emeb/orangecrab_adc/gateware/verilog/src/tuner_slice_1k.v

// tuner_slice_1k.v - one leg of real->complex tuner with 4k sine cycle
// 07-18-16 E. Brombaugh

module tuner_slice_1k #(
    parameter dsz = 14,
              psz = 12
)
(
    input clk, reset, shf_90,
    input signed [dsz-1:0] in,
    input [psz-1:0] phs,
    output reg signed [dsz-1:0] out
);
    // split acc into quadrant and address and delay sign bit
    wire [1:0] p_quad = phs[psz-1:psz-2] + {1'b0,shf_90};
    reg [1:0] quad;
    reg [psz-3:0] addr;
    reg sincos_sign;
    always @(posedge clk)
    begin
        if(reset == 1'b1)
        begin
            quad <= 2'b0;
            addr <= 8'b0;
            sincos_sign <= 1'b0;
        end
        else
        begin
            quad <= p_quad;
            addr <= phs[psz-3:0] ^ {psz-2{p_quad[0]}};
            sincos_sign <= quad[1];
        end
    end
    
    // look up 1/4 cycle sine
    reg signed [15:0] sine_lut[0:1023];
    reg signed [15:0] sincos_raw;
    initial
    begin
        $readmemh("../src/sine_table_1k.memh", sine_lut);
    end
    always @(posedge clk)
    begin
        sincos_raw <= sine_lut[addr];
    end
    
    // invert sign of lut output and delay to align
    reg signed [15:0] sincos_p, sincos;
    reg sincos_sign_d1;
    always @(posedge clk)
    begin
        if(reset == 1'b1)
        begin
            sincos <= 16'h0000;
            sincos_p <= 16'h0000;
            sincos_sign_d1 <= 0;
        end
        else
        begin
            sincos_sign_d1 <= sincos_sign;
            sincos_p <= sincos_raw;
            sincos <= sincos_sign_d1 ? -sincos_p : sincos_p;
        end
    end
    
    // multiply, round, saturate
    reg signed [dsz+16-1:0] mult;
    reg signed [dsz+1:0] out_rnd;
    wire signed [dsz-1:0] out_sat;
    
    sat #(.isz(dsz+1),.osz(dsz))
        u_sat(.in(out_rnd[dsz+1:1]),.out(out_sat));
    
    always @(posedge clk)
    begin
        if(reset == 1'b1)
        begin
            mult <= 0;
            out_rnd <= 0;
            out <= 0;
        end
        else
        begin
            mult <= in * sincos;
            out_rnd <= mult[dsz+16-1:14] + 1;
            out <= out_sat;
        end
    end
endmodule
